Mark-271/kitchen-clock-poc/schematic/kicad/circuit.sch

## KiCad design schematic/kicad/circuit.sch (2022-02-04, an earlier design)

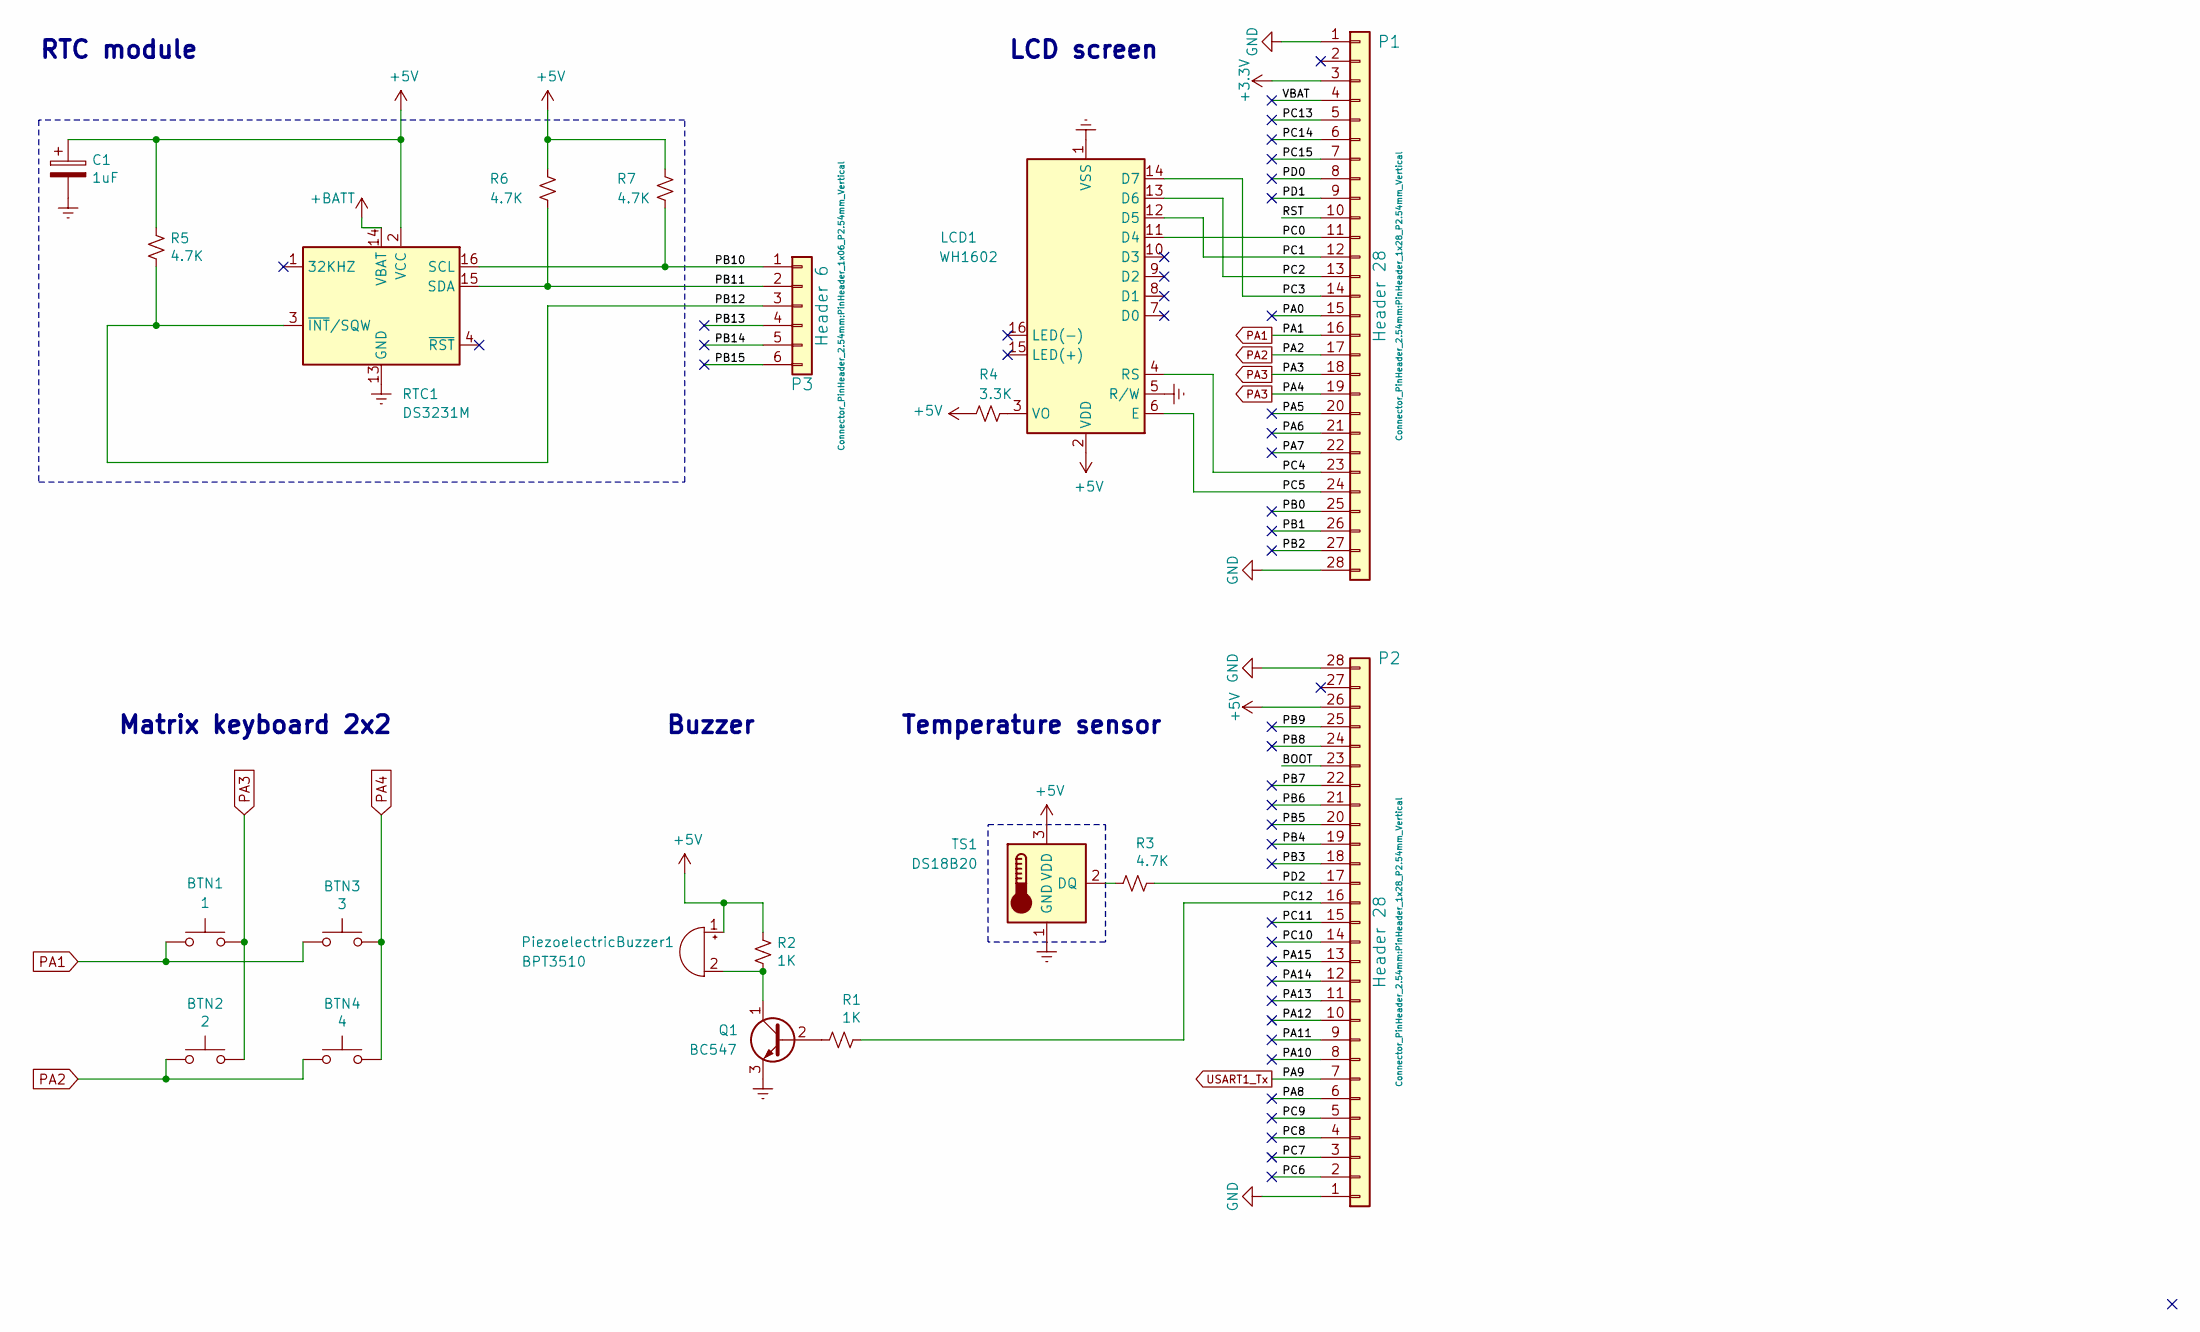
[picture p5: schematic circuit.sch]

Parts:
BTN1: 1
BTN2: 2
BTN3: 3
BTN4: 4
C1: 1uF
LCD1: WH1602; WC1602A
P1, P2: Header 28; PinHeader_1x28_P2.54mm_Vertical
P3: Header 6; PinHeader_1x06_P2.54mm_Vertical
PiezoelectricBuzzer1: BPT3510
Q1: BC547; TO-92_Inline
R1, R2: 1K
R3, R5, R6, R7: 4.7K
R4: 3.3K
RTC1: DS3231M; SOIC-16W_7.5x10.3mm_P1.27mm
TS1: DS18B20; TO-92_Inline

Connections:
+3.3V: P1.3
+5V: C1.1, LCD1.2 (VDD), P2.26, PiezoelectricBuzzer1.1 (-), R2.1, R4.2, R5.1, R6.1, R7.1, RTC1.2 (VCC), TS1.3 (VDD)
+BATT: RTC1.14 (VBAT)
BOOT: P2.23
Earth: C1.2, LCD1.1 (VSS), LCD1.5 (R/W), Q1.3 (E), RTC1.5 (GND), RTC1.6 (GND), RTC1.7 (GND), RTC1.8 (GND), RTC1.9 (GND), RTC1.10 (GND), RTC1.11 (GND), RTC1.12 (GND), RTC1.13 (GND), TS1.1 (GND)
GND: P1.1, P1.28, P2.1, P2.28
unnamed: LCD1.3 (VO), R4.1
unnamed: PiezoelectricBuzzer1.2 (+), Q1.1 (C), R2.2
unnamed: Q1.2 (B), R1.2
unnamed: R3.2, TS1.2 (DQ)
PA0: P1.15
PA1: BTN1.1, BTN3.1, P1.16
PA2: BTN2.1, BTN4.1, P1.17
PA3: BTN1.2, BTN2.2, P1.18, P1.19
PA4: BTN3.2, BTN4.2
PA5: P1.20
PA6: P1.21
PA7: P1.22
PA8: P2.6
PA10: P2.8
PA11: P2.9
PA12: P2.10
PA13: P2.11
PA14: P2.12
PA15: P2.13
PB0: P1.25
PB1: P1.26
PB2: P1.27
PB3: P2.18
PB4: P2.19
PB5: P2.20
PB6: P2.21
PB7: P2.22
PB8: P2.24
PB9: P2.25
PB10: P3.1, R7.2, RTC1.16 (SCL)
PB11: P3.2, R6.2, RTC1.15 (SDA)
PB12: P3.3, R5.2, RTC1.3 (~INT~/SQW)
PB13: P3.4
PB14: P3.5
PB15: P3.6
PC0: LCD1.11 (D4), P1.11
PC1: LCD1.12 (D5), P1.12
PC2: LCD1.13 (D6), P1.13
PC3: LCD1.14 (D7), P1.14
PC4: LCD1.4 (RS), P1.23
PC5: LCD1.6 (E), P1.24
PC6: P2.2
PC7: P2.3
PC8: P2.4
PC9: P2.5
PC10: P2.14
PC11: P2.15
PC12: P2.16, R1.1
PC13: P1.5
PC14: P1.6
PC15: P1.7
PD0: P1.8
PD1: P1.9
PD2: P2.17, R3.1
RST: P1.10
USART1_Tx: P2.7
VBAT: P1.4

Notes on the sheet:
Matrix keyboard 2x2
Buzzer
RTC module
LCD screen
Temperature sensor
