Mark-271/kitchen-clock-poc/include/config.h

#ifndef CONFIG_H
#define CONFIG_H

/* Serial console */
#define CONFIG_SERIAL_CONSOLE
#define CONFIG_SERIAL_SPEED		115200
/* Catch sbrk() syscall when CONFIG_SERIAL_CONSOLE is disabled */
/* #define CONFIG_SERIAL_SBRK_TRAP */
/* Messages with level less than this will be printed to the console; 1-8 */
#define CONFIG_LOGLEVEL			4

/* Vector table size (=sizeof(vector_table) */
#define CONFIG_VTOR_SIZE		0x150

/* GPIO level transient time, usec */
#define CONFIG_GPIO_STAB_DELAY		10

/* ---- Watchdog timer ---- */
/* Enable watchdog timer */
#define CONFIG_WDT
/* Watchdog timer period, msec */
#define CONFIG_WDT_PERIOD		1000

#endif /* CONFIG_H */
