Mark-271/kitchen-clock-poc/include/melody.h

/* SPDX-License-Identifier: GPL-3.0-or-later */
/*
 * Author: Mark Sungurov <mark.sungurov@gmail.com>
 */

#ifndef MELODY_H
#define MELODY_H

#include <note.h>
#include <stddef.h>

extern const struct note melody_alarm[];
extern const size_t melody_alarm_len;

#endif /* MELODY_H */
