Mark-271/kitchen-clock-poc/include/ds18b20.h

#ifndef DS18B20_H
#define DS18B20_H

#include <one_wire.h>
#include <stdint.h>

/* Contains parsed data from DS18B20 temperature sensor */
struct ds18b20_temp {
	uint16_t integer:12;
	uint16_t frac;
	char sign;		/* '-' or '+' */
};

struct ds18b20 {
	uint32_t port;
	uint16_t pin;
	struct ds18b20_temp temp;
};

int ds18b20_init(struct ds18b20 *obj);
void ds18b20_exit(struct ds18b20 *obj);
struct ds18b20_temp ds18b20_read_temp(struct ds18b20 *obj);
char *ds18b20_temp2str(struct ds18b20_temp *obj, char str[]);

#endif /* DS18B20_H */
