Mark-271/kitchen-clock-poc/include/one_wire.h

#ifndef ONE_WIRE_H
#define ONE_WIRE_H

#include <stdint.h>

struct ow {
	uint32_t port;
	uint16_t pin;
};

int ow_init(struct ow *obj);
void ow_exit(struct ow *obj);
int ow_reset_pulse(struct ow *obj);
void ow_write_byte(struct ow *obj, uint8_t byte);
int8_t ow_read_byte(struct ow *obj);

#endif /* ONE_WIRE_H */
